shaafshahzad/fresh-first/hardware/enclosure/output/fresh-first-case-preview.png

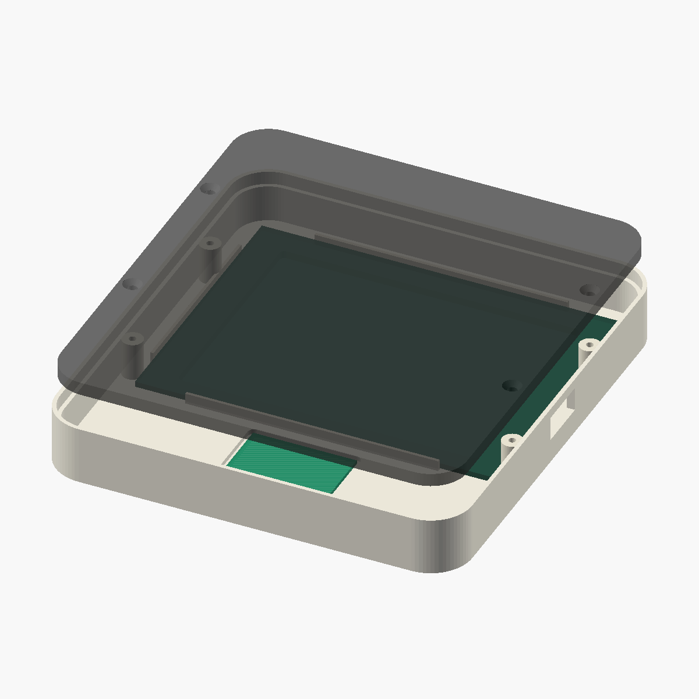
hardware/enclosure/output/fresh-first-case-preview.png
