shaafshahzad/fresh-first/hardware/enclosure/output/fresh-first-product-preview.png

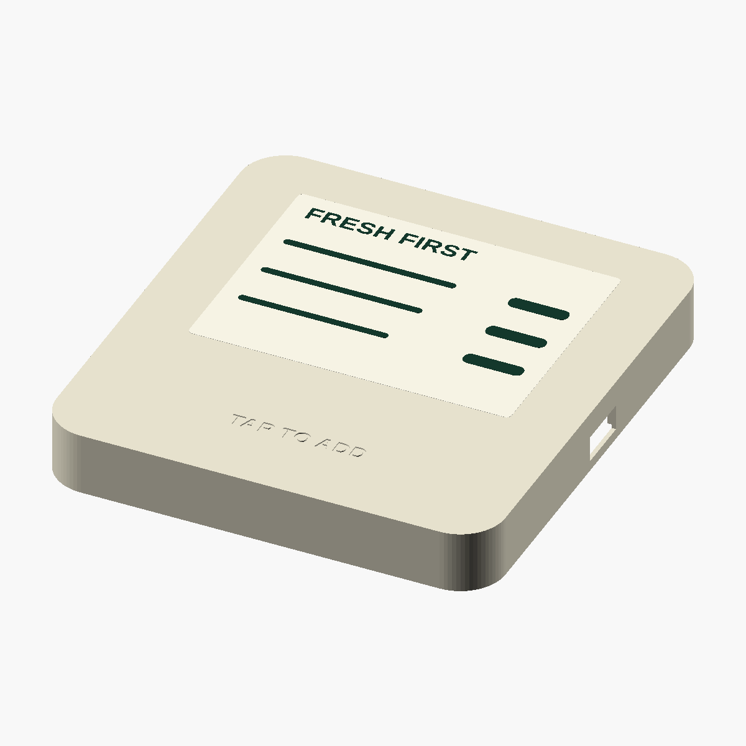
hardware/enclosure/output/fresh-first-product-preview.png
