shaafshahzad/fresh-first/hardware/firmware/include/root_ca.h

#pragma once

// Google Trust Services Root R1. The production Vercel endpoint currently
// chains to this root. Valid through June 2036.
static constexpr char kRootCa[] = R"CERT(
-----BEGIN CERTIFICATE-----
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
bP6MvPJwNQzcmRk13NfIRmPVNnGuV/u3gm3c
-----END CERTIFICATE-----
)CERT";
